radiolok/lamptest/firmware/lampdb.c

#include <string.h>
#include <avr/eeprom.h>
#include <avr/pgmspace.h>
#include "lampdb.h"

// Name, Uh, Ih, Ug1, Ua, Ia, Ug2, Ig2, S, R, K
static const lamp_t lamprom[LAMP_FLASH_COUNT] PROGMEM = {
        {'P','w','r','S','u','p','p','l','y',  0,  0,240,  0,   0,  0,   0,  0,  0,  0 },
        {'F','o','r','F','u','t','U','s','e',  0,  0,240,  0,   0,  0,   0,  0,  0,  0 },
        {'E','C','C','8','1','_','G','1','1',126,  0, 20,250, 100,  0,   0, 55,110,600 },
        {'E','C','C','8','1','_','G','2','1',126,  0, 20,250, 100,  0,   0, 55,110,600 },
        {'E','C','C','8','2','_','G','1','1',126,  0, 85,250, 105,  0,   0, 22, 77,170 },
        {'E','C','C','8','2','_','G','2','1',126,  0, 85,250, 105,  0,   0, 22, 77,170 },
        {'E','C','C','8','3','_','G','1','1',126,  0, 20,250,  12,  0,   0, 16,625,999 },
        {'E','C','C','8','3','_','G','2','1',126,  0, 20,250,  12,  0,   0, 16,625,999 },
        {'E','C','C','8','8','_','G','1','1', 63,  0, 13, 90, 150,  0,   0,125, 26,330 },
        {'E','C','C','8','8','_','G','2','1', 63,  0, 13, 90, 150,  0,   0,125, 26,330 },
        {'6','N','1','P','_','_','G','1','1', 63,  0, 40,250,  75,  0,   0, 45,  0,350 },
        {'6','N','1','P','_','_','G','2','1', 63,  0, 40,250,  75,  0,   0, 45,  0,350 },
        {'6','N','2','P','_','_','G','1','1', 63,  0, 15,250,  23,  0,   0, 21,  0,999 },
        {'6','N','2','P','_','_','G','2','1', 63,  0, 15,250,  23,  0,   0, 21,  0,999 },
        {'6','N','6','P','_','_','G','1','1', 63,  0, 20,120, 300,  0,   0,110, 19,200 },
        {'6','N','6','P','_','_','G','2','1', 63,  0, 20,120, 300,  0,   0,110, 19,200 },
        {'6','N','3','0','P','_','G','1','1', 63,  0, 22, 80, 400,  0,   0,180,  0,150 },
        {'6','N','3','0','P','_','G','2','1', 63,  0, 22, 80, 400,  0,   0,180,  0,150 },
        {'6','S','L','7','_','_','I','1','2', 63,  0, 20,250,  23,  0,   0, 16,440,700 },
        {'6','S','L','7','_','_','I','2','2', 63,  0, 20,250,  23,  0,   0, 16,440,700 },
        {'6','S','N','7','_','_','I','1','2', 63,  0, 80,250,  90,  0,   0, 26, 77,200 },
        {'6','S','N','7','_','_','I','2','2', 63,  0, 80,250,  90,  0,   0, 26, 77,200 },
        {'6','A','S','7','_','_','I','1','5', 63,  0,200, 80,1100,  0,   0,  0,  0,  0 },
        {'6','A','S','7','_','_','I','2','5', 63,  0,200, 80,1100,  0,   0,  0,  0,  0 },
        {'6','S','1','9','P','_','H','0','2', 63,  0,150, 90,1000,  0,   0,  0,  0,  0 },
        {'E','F','8','6','_','_','E','0','1', 63,  0, 20,250,  30,140,  60, 19,999,380 },
        {'6','S','J','7','_','_','D','0','2', 63,  0, 30,250,  30,100,  80, 17,999,  0 },
        {'E','L','8','4','_','_','B','0','2', 63,  0, 73,250, 480,250, 550,113,400,190 },
        {'6','V','6','S','_','_','A','0','2', 63,  0,125,250, 450,250, 500, 41,500,  0 },
        {'6','F','6','S','_','_','A','0','2', 63,  0,200,285, 380,285, 700, 25,500,  0 },
        {'6','L','6','G','_','_','A','0','3', 63,  0,140,250, 720,250, 500,  0,225,  0 },
        {'E','L','3','4','_','_','A','0','5', 63,  0,135,250,1000,265,1490,110,150,110 },
        {'K','T','6','6','_','_','A','0','5', 63,  0,150,250, 850,250, 700, 60,225,  0 },
        {'K','T','7','7','_','_','A','0','5', 63,  0,150,250,1000,250,1000,105,230,115 },
        {'K','T','8','8','_','_','A','0','5', 63,  0,150,250,1400,250, 700,115,120, 80 },
        {'6','P','1','P','_','_','C','0','2', 63,  0,125,250, 450,250, 700, 45,500,  0 },
        {'E','L','9','0','_','_','F','0','1', 63,  0,125,250, 450,250, 450, 41,520,  0 },
        {'E','L','9','5','_','_','F','0','1', 63,  0, 90,250, 240,250, 450, 50,800,170 },
        {'P','C','L','8','6','T','J','1','2',  0, 30, 17,230,  12,  0,   0, 16,620,990 },
        {'P','C','L','8','6','P','J','2','2',  0, 30, 57,230, 390,230, 650,105,450,999 },
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
};

// EEPROM layout: the user table, followed by the last selected slot.
typedef struct {
    lamp_t  user[LAMP_USER_COUNT];
    uint8_t last;
} eeprom_layout_t;

// Names are indexes into AZ[]
static eeprom_layout_t ee EEMEM = {
    .user = {
        { 33, 13, 28, 32, 18, 26,  9, 28, 28, 63,  0, 90,100,  90,  0,   0, 56,  0,  0 },
        { 33, 13, 28, 32, 18, 26,  9, 29, 28, 63,  0, 90,100,  90,  0,   0, 56,  0,  0 },
        {  4,  1, 11, 29, 28, 26,  9, 27, 29, 63,  0, 60,250, 360,250, 450, 90,500,230 },
        {  4,  5, 29, 28, 26, 26,  9, 27, 29, 63,  0, 20,250,  60,250, 200, 45,999,  0 },
        {  4,  5, 35, 27, 33, 26,  4, 27, 28, 63,  0, 22,250,  30,140,  60, 22,999,380 },
        {  4,  5, 35, 27, 26, 26,  9, 27, 28, 63,  0, 20,175, 100,175,   0, 72,  0,  0 },
        {  4,  5, 35, 32, 26, 26,  9, 27, 28, 63,  0, 20,250, 100,100, 250, 60,999,260 },
        {  4,  5, 35, 36, 26, 26,  9, 27, 28, 63,  0, 20,250,  90,100, 300, 36,999,  0 },
        { 34, 27, 29, 34, 26, 26,  9, 27, 32, 63,  0,140,250, 720,250, 500,  0,225,  0 },
        { 34, 32, 35, 28, 26, 26,  0, 27, 32, 63,  0,140,250, 720,250, 500, 60,225,  0 },
        { 34, 32, 36, 28, 26, 26,  9, 27, 32, 63,  0,100,290, 600,290, 800,102,290,168 },
        {  4, 11, 30, 33, 26, 26,  9, 27, 32, 63,  0, 82,100,1000,100, 700,140, 50, 56 },
        { 33,  9, 34, 26, 26, 26,  9, 27, 29, 63,  0, 30,250,  20,100,  50, 12,  0,  0 },
        {  4, 11, 35, 29, 26, 26,  1, 27, 29, 63,  0,104,170, 530,170,1000, 90,200,100 },
        {  4, 11, 35, 33, 26, 26,  1, 27, 29, 63,  0,125,170, 700,170, 500,100,230, 80 },
        { 33, 15, 28, 32, 15, 26,  9, 27, 29, 63,  0, 35,280, 310,170, 500,150,999, 70 },
        { 33, 25, 31, 15, 26, 26,  9, 27, 29, 63,  0, 10,250, 108,150, 430, 52,999,410 },
        { 33, 15, 34, 18, 26, 26,  9, 27, 30, 63,  0,140,250, 720,250, 800, 59,999, 85 },
        { 33, 15, 36, 26, 26, 26,  9, 27, 29, 63,  0, 60,250, 300,250, 300, 70,600,  0 },
    },
    .last = LAMP_SUPPLY,
};

static lamp_t *user_record(uint8_t num)
{
    return &ee.user[num - LAMP_FLASH_COUNT];
}

void lampdb_load(uint8_t num, lamp_t *lamp)
{
    if (lamp_is_user(num))
        eeprom_read_block(lamp, user_record(num), sizeof(lamp_t));
    else
        memcpy_P(lamp, &lamprom[num], sizeof(lamp_t));
}

void lampdb_reload_name(uint8_t num, lamp_t *lamp)
{
    eeprom_read_block(lamp->name, user_record(num)->name, NAME_SECTION);
}

void lampdb_save_field(uint8_t num, const lamp_t *lamp, uint8_t field)
{
    uint8_t off = lamp_field_offset(field);
    uint8_t *dst = (uint8_t *)user_record(num) + off;
    const uint8_t *src = (const uint8_t *)lamp + off;

    if (lamp_field_is_word(field))
        eeprom_update_word((uint16_t *)dst, *(const uint16_t *)src);
    else
        eeprom_update_byte(dst, *src);
}

uint8_t lampdb_last(void)
{
    uint8_t num = eeprom_read_byte(&ee.last);
    return (num < LAMP_COUNT) ? num : LAMP_SUPPLY; // erased EEPROM reads 0xFF
}

void lampdb_set_last(uint8_t num)
{
    eeprom_update_byte(&ee.last, num);
}
